alinxalinx/Z7_P/linux/.images_for_documents/4.png

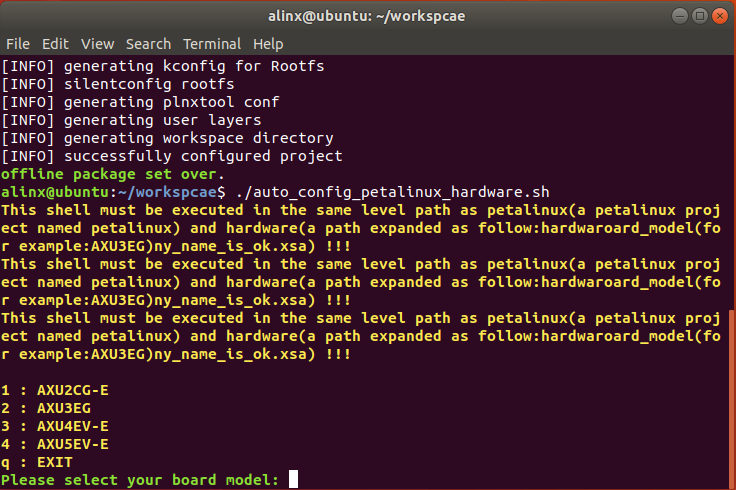
linux/.images_for_documents/4.png
