alinxalinx/Z7_P/linux/.images_for_documents/5.png

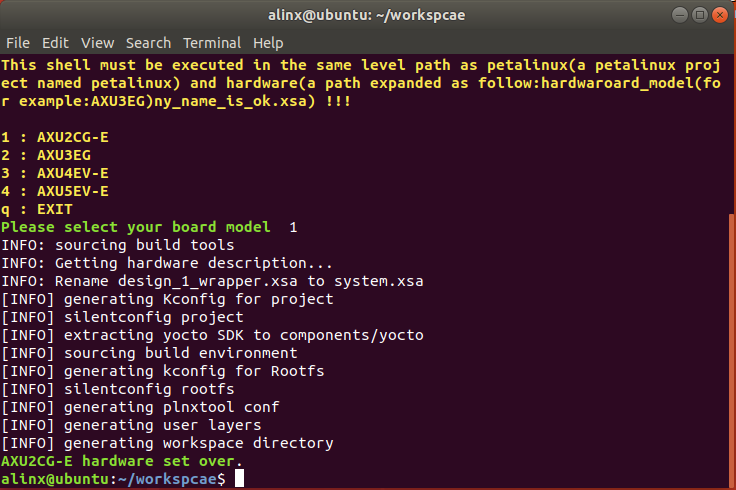
linux/.images_for_documents/5.png
