alinxalinx/Z7_P/linux/.images_for_documents/8.png

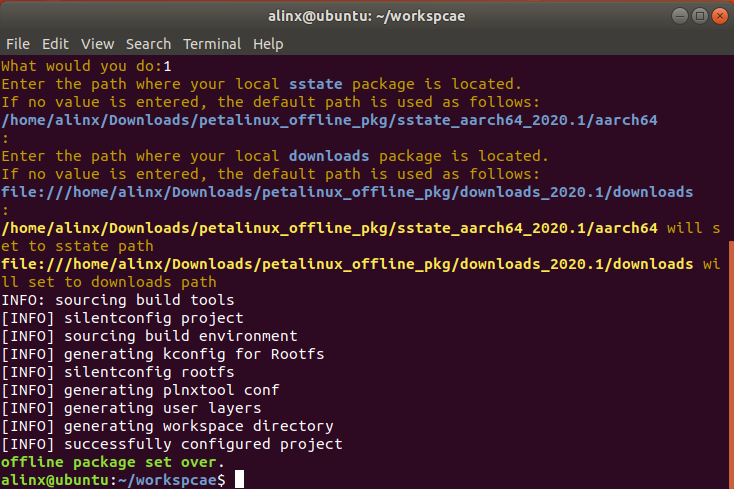
linux/.images_for_documents/8.png
