alinxalinx/Z7_P/linux/.images_for_documents/9.png

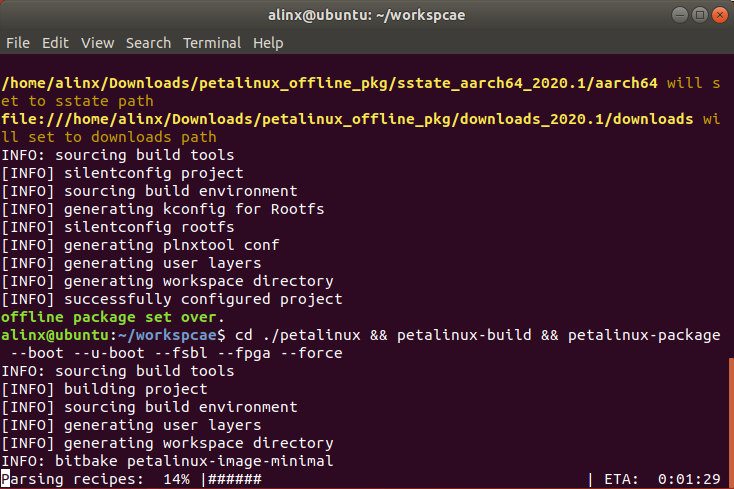
linux/.images_for_documents/9.png
