alinxalinx/Z7_P/linux/.images_for_documents/10.png

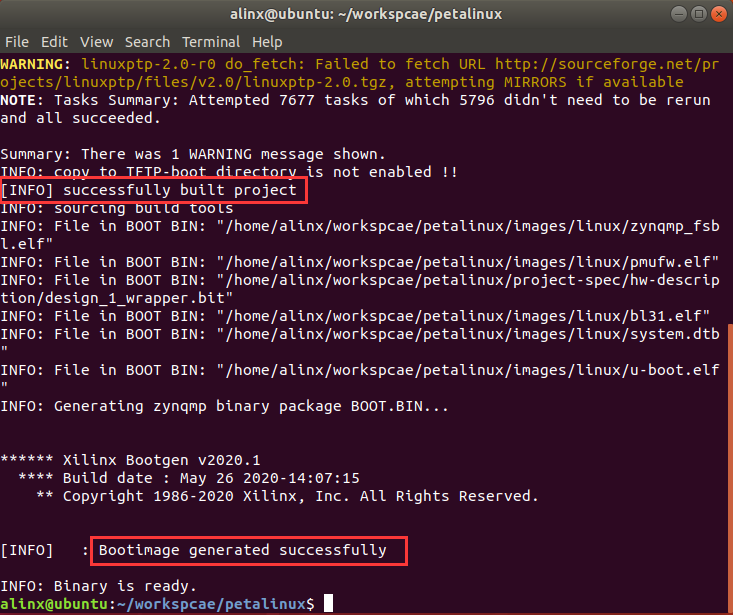
linux/.images_for_documents/10.png
