alinxalinx/Z7_P/linux/.images_for_documents/11.png

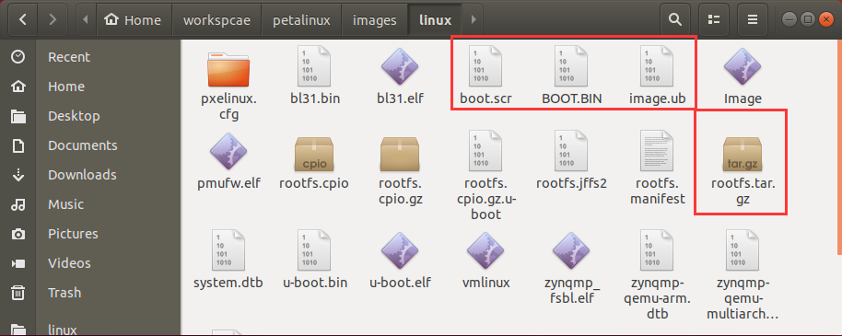
linux/.images_for_documents/11.png
