alinxalinx/Z7_P/linux/.images_for_documents/13.png

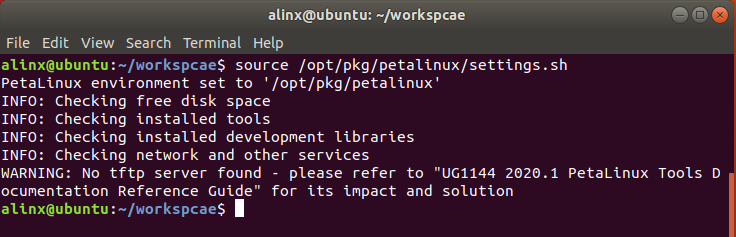
linux/.images_for_documents/13.png
