alinxalinx/Z7_P/linux/.images_for_documents/15.png

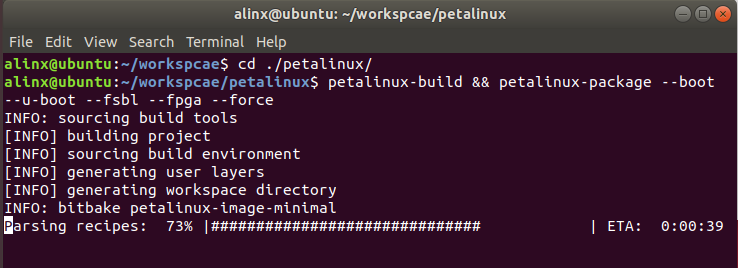
linux/.images_for_documents/15.png
