alinxalinx/Z7_P/vivado/auto_create_project/src/constraints/gpio.xdc

set_property PACKAGE_PIN M9 [get_ports {leds_tri_o[0]}]
set_property PACKAGE_PIN K8 [get_ports {leds_tri_o[1]}]
set_property PACKAGE_PIN L8 [get_ports {leds_tri_o[2]}]
set_property IOSTANDARD LVCMOS33 [get_ports {leds_tri_o[*]}]

set_property PACKAGE_PIN J9 [get_ports {keys_tri_i[0]}]
set_property IOSTANDARD LVCMOS33 [get_ports {keys_tri_i[*]}]
