alinxalinx/Z7_P/vivado/auto_create_project/src/constraints/uart.xdc

set_property PACKAGE_PIN N8 [get_ports {uart_rxd}]
set_property IOSTANDARD LVCMOS33 [get_ports {uart_rxd}]

set_property PACKAGE_PIN N9 [get_ports {uart_txd}]
set_property IOSTANDARD LVCMOS33 [get_ports {uart_txd}]
